Envious-Data/EnvOpenClock/Firmware/display.c

#include <math.h>
#include <stdbool.h>
#include <stdio.h>
#include <stdlib.h>
#include <string.h>

#include "display.h"
#include "hardware/i2c.h"
#include "pico/stdlib.h"

#define I2C_DISPLAY_LINE i2c1
#define I2C_DISPLAY_SDA 26
#define I2C_DISPLAY_SCL 27

#define MODE_ADDR 0b00000000
#define BRIGHTNESS_ADDR 0b00011001
#define UPDATE_ADDR 0b00001100
#define OPTION_ADDR 0b00001101
#define MATRIX_A_ADDR 0b00001110
#define MATRIX_B_ADDR 0b00000001

#define DEFAULT_MODE 0b00011000
#define DEFAULT_OPTIONS 0b00001110

//uint8_t brightness_level = 0b00011001;
uint8_t brightness_level = 0b00111111; // original brightness.


/**
 * @brief The addresses of the displays in order from left to right.
    They are doubled up since there are 2 displays per chip.
 */
uint8_t addresses[8] = {0x63, 0x63, 0x60, 0x60, 0x62, 0x62, 0x61, 0x61};

/**
 * @brief
 *
 */
uint8_t displays[8][8] = {{0b00000000, 0b00000000, 0b00000000, 0b00000000,
                           0b00000000, 0b00000000, 0b00000000, 0b00000000},
                          {0b00000000, 0b00000000, 0b00000000, 0b00000000,
                           0b00000000, 0b00000000, 0b00000000, 0b00000000},
                          {0b00000000, 0b00000000, 0b00000000, 0b00000000,
                           0b00000000, 0b00000000, 0b00000000, 0b00000000},
                          {0b00000000, 0b00000000, 0b00000000, 0b00000000,
                           0b00000000, 0b00000000, 0b00000000, 0b00000000},
                          {0b00000000, 0b00000000, 0b00000000, 0b00000000,
                           0b00000000, 0b00000000, 0b00000000, 0b00000000},
                          {0b00000000, 0b00000000, 0b00000000, 0b00000000,
                           0b00000000, 0b00000000, 0b00000000, 0b00000000},
                          {0b00000000, 0b00000000, 0b00000000, 0b00000000,
                           0b00000000, 0b00000000, 0b00000000, 0b00000000},
                          {0b00000000, 0b00000000, 0b00000000, 0b00000000,
                           0b00000000, 0b00000000, 0b00000000, 0b00000000}};

/**
 * @brief Contains 8x8 bit patterns which correlate to various symbols
    which may need to be displayed on the LTP-305's.

    ASCII Based

    @example
    The symbol "+"
    #Col   1 2 3 4 5
    0b00000000, # Row 1
    0b00000000, # Row 2
    0b00000000, # Row 3
    0b00000000, # Row 4
    0b00000000, # Row 5
    0b00000000, # Row 6
    0b10000000, # Row 7, bit 8 =  decimal place
    0b00000000

    The array { 0x08, 0x08, 0x3e, 0x08, 0x08, 0x00, 0x00, 0x00 }
    0b00001000,
    0b00001000,
    0b00111110,
    0b00001000,
    0b00001000,
    0b00000000,
    0b00000000,
    0b00000000
 */
uint8_t characters[][8] = {
    {0x00, 0x00, 0x00, 0x00, 0x00, 0x00, 0x00, 0x00},  // (space)
    {0x00, 0x00, 0x5f, 0x00, 0x00, 0x00, 0x00, 0x00},  // !
    {0x00, 0x07, 0x00, 0x07, 0x00, 0x00, 0x00, 0x00},  // "
    {0x14, 0x7f, 0x14, 0x7f, 0x14, 0x00, 0x00, 0x00},  // #
    {0x24, 0x2a, 0x7f, 0x2a, 0x12, 0x00, 0x00, 0x00},  // $
    {0x23, 0x13, 0x08, 0x64, 0x62, 0x00, 0x00, 0x00},  // %
    {0x36, 0x49, 0x55, 0x22, 0x50, 0x00, 0x00, 0x00},  // &
    {0x00, 0x05, 0x03, 0x00, 0x00, 0x00, 0x00, 0x00},  // '
    {0x00, 0x1c, 0x22, 0x41, 0x00, 0x00, 0x00, 0x00},  // (
    {0x00, 0x41, 0x22, 0x1c, 0x00, 0x00, 0x00, 0x00},  // )
    {0x08, 0x2a, 0x1c, 0x2a, 0x08, 0x00, 0x00, 0x00},  // *
    {0x08, 0x08, 0x3e, 0x08, 0x08, 0x00, 0x00, 0x00},  // +
    {0x00, 0x50, 0x30, 0x00, 0x00, 0x00, 0x00, 0x00},  // ,
    {0x08, 0x08, 0x08, 0x08, 0x08, 0x00, 0x00, 0x00},  // -
    {0x00, 0x60, 0x60, 0x00, 0x00, 0x00, 0x00, 0x00},  // .
    {0x20, 0x10, 0x08, 0x04, 0x02, 0x00, 0x00, 0x00},  // /
    {0x3e, 0x51, 0x49, 0x45, 0x3e, 0x00, 0x00, 0x00},  // 0
    {0x00, 0x42, 0x7f, 0x40, 0x00, 0x00, 0x00, 0x00},  // 1
    {0x42, 0x61, 0x51, 0x49, 0x46, 0x00, 0x00, 0x00},  // 2
    {0x21, 0x41, 0x45, 0x4b, 0x31, 0x00, 0x00, 0x00},  // 3
    {0x18, 0x14, 0x12, 0x7f, 0x10, 0x00, 0x00, 0x00},  // 4
    {0x27, 0x45, 0x45, 0x45, 0x39, 0x00, 0x00, 0x00},  // 5
    {0x3c, 0x4a, 0x49, 0x49, 0x30, 0x00, 0x00, 0x00},  // 6
    {0x01, 0x71, 0x09, 0x05, 0x03, 0x00, 0x00, 0x00},  // 7
    {0x36, 0x49, 0x49, 0x49, 0x36, 0x00, 0x00, 0x00},  // 8
    {0x06, 0x49, 0x49, 0x29, 0x1e, 0x00, 0x00, 0x00},  // 9
    {0x00, 0x36, 0x36, 0x00, 0x00, 0x00, 0x00, 0x00},  // :
    {0x00, 0x56, 0x36, 0x00, 0x00, 0x00, 0x00, 0x00},  // ;
    {0x00, 0x08, 0x14, 0x22, 0x41, 0x00, 0x00, 0x00},  // <
    {0x14, 0x14, 0x14, 0x14, 0x14, 0x00, 0x00, 0x00},  // =
    {0x41, 0x22, 0x14, 0x08, 0x00, 0x00, 0x00, 0x00},  // >
    {0x02, 0x01, 0x51, 0x09, 0x06, 0x00, 0x00, 0x00},  // ?
    {0x32, 0x49, 0x79, 0x41, 0x3e, 0x00, 0x00, 0x00},  // @
    {0x7e, 0x11, 0x11, 0x11, 0x7e, 0x00, 0x00, 0x00},  // A
    {0x7f, 0x49, 0x49, 0x49, 0x36, 0x00, 0x00, 0x00},  // B
    {0x3e, 0x41, 0x41, 0x41, 0x22, 0x00, 0x00, 0x00},  // C
    {0x7f, 0x41, 0x41, 0x22, 0x1c, 0x00, 0x00, 0x00},  // D
    {0x7f, 0x49, 0x49, 0x49, 0x41, 0x00, 0x00, 0x00},  // E
    {0x7f, 0x09, 0x09, 0x01, 0x01, 0x00, 0x00, 0x00},  // F
    {0x3e, 0x41, 0x41, 0x51, 0x32, 0x00, 0x00, 0x00},  // G
    {0x7f, 0x08, 0x08, 0x08, 0x7f, 0x00, 0x00, 0x00},  // H
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
};

/**
 * @brief In order for characters to be displayed on the second display they
    will need to be translated into the correct bit pattern. This is since
    the first matrix is represented by the 8 byte buffer in the form

    #Col   1 2 3 4 5
    0b00000000, # Row 1
    0b00000000, # Row 2
    0b00000000, # Row 3
    0b00000000, # Row 4
    0b00000000, # Row 5
    0b00000000, # Row 6
    0b10000000, # Row 7, bit 8 =  decimal place
    0b00000000

    This is compared to the second display which is represented as the first
    but reflected in the line y=x.

    #Row 8 7 6 5 4 3 2 1
    0b01111111, # Col 1, bottom to top
    0b01111111, # Col 2
    0b01111111, # Col 3
    0b01111111, # Col 4
    0b01111111, # Col 5
    0b00000000,
    0b00000000,
    0b01000000  # bit 7, decimal place

    To save on processing time these are precalculated at the start of the
    program.
 */
uint8_t alternate_characters[count_of(characters)][8];

/**
 * @brief A helper function to add an amount num_chars to of a specific
 character character_to_append to the end of a string.

    This is used to add whitespace to the end of a scrolling string.
 *
 * @param original The original string to have letters appended to.
 * @param character_to_append The character to append to the string
 * @param num_chars The number of character_to_append to be appended
 *
 * @return char* The new string
 */
char *append_chars(const char *original, char character_to_append,
                   size_t num_chars) {
  size_t original_length = strlen(original);
  char *new_string = (char *)malloc(original_length + num_chars +
                                    1);  // Don't forget +1 for null terminator

  if (new_string == NULL) {
    return NULL;  // Memory allocation failed
  }

  // Copy the original string into the new longer one
  strcpy(new_string, original);

  // Append desired amount of characters
  for (size_t i = 0; i < num_chars; i++) {
    new_string[original_length + i] = character_to_append;
  }

  new_string[original_length + num_chars] = '\0';  // Null-terminate the string

  return new_string;
}

/**
 * @brief This is another helper function that converts an array of
    uint8_t's from a left matrix, the one defined with columns
    v rows into a right matrix in the form rows v columns.

    Essentially this is a reflection in the line y=x of a 2D matrix.
 *
 * @param left_matrix The original matrix in the form columns vs rows
 * @param right_matrix The generated matrix in the form rows vs columns
 */
void convertLeftToRight(const uint8_t *left_matrix, uint8_t *right_matrix) {
  for (int row = 0; row < 8; row++) {
    for (int col = 0; col < 8; col++) {
      uint8_t bit_value = (left_matrix[row] >> (col)) & 1;
      right_matrix[col] |= (bit_value << row);
    }
  }
}

/**
 * @brief This MUST be called at the start of the program otherwise the
    letters for the right matrix will not be generated and will
    not display properly if at all.
 */
void pre_generate_alternate_characters() {
  for (int i = 0; i < count_of(characters); i++) {
    convertLeftToRight(characters[i], alternate_characters[i]);
  }
}

/**
 * @brief Set the option function is used to change a setting on the
    IS31FL3730-QFLS2-TR chips such as brightness or a configuration setting.
 *
 * @param display The 0 indexed display to update [0,8)
 * @param address The address of the register to update on the IS31FL3730
 * @param value The value to send over i2c to the register
 */
void set_option(int display, uint8_t address, uint8_t value) {
  if (display < 0 || display > 7) return;

  uint8_t buf[2];

  buf[0] = address;
  buf[1] = value;

  i2c_write_timeout_us(I2C_DISPLAY_LINE, addresses[display], buf, count_of(buf),
                       false, 1000);
}

/**
 * @brief This is used when updating the displays, in order to update specific
 rows a certain address must be used before the buffer. This function prepends
 this address.
 *
 * @param address The address of the register to be prepended to the start of
 the buffer
 * @param buffer The pointer to the current buffer to have an address prepended
 * @param buffer_size The size of the buffer to be prepended
 *
 * @return uint8_t* The pointer in memory of the new altered buffer
 */
uint8_t *prepend_address(uint8_t address, uint8_t *buffer, int buffer_size) {
  int new_buffer_size = buffer_size + 1;

  uint8_t *new_buffer = (uint8_t *)malloc(new_buffer_size * sizeof(uint8_t));

  if (new_buffer == NULL) {
    return NULL;
  }

  new_buffer[0] = address;

  for (int i = 0; i < buffer_size; i++) {
    new_buffer[i + 1] = buffer[i];
  }

  return new_buffer;
}

/**
 * @brief Used to update all displays all at once. Once called it will push
    what is currently stored in displays to each of the 4 IS31FL3730's
 */
void update_display() {
  // printf("update_display called\n");  // Add this line
  for (int i = 0; i < count_of(displays); i++) {
    uint8_t mat_addr = i % 2 == 0 ? MATRIX_A_ADDR : MATRIX_B_ADDR;

    uint8_t *pre_mat_buf =
        prepend_address(mat_addr, displays[i], count_of(displays[i]));
    i2c_write_timeout_us(I2C_DISPLAY_LINE, addresses[i], pre_mat_buf,
                         count_of(displays[i]) + 1, false, 1000);
    free(pre_mat_buf);

    if (i % 2 != 0) {
      set_option(i, MODE_ADDR, DEFAULT_MODE);
      set_option(i, OPTION_ADDR, DEFAULT_OPTIONS);
      set_option(i, BRIGHTNESS_ADDR, brightness_level);
      set_option(i, UPDATE_ADDR, 0b00000001);
    }
  }
}

/**
 * @brief Set a specific pixel on a display to on or off.
 *
 * @param display The 0 indexed display to update [0,8)
 * @param x The 0 indexed x value of the pixel to be updated [0, 5)
 * @param y The 0 indexed y value of the pixel to be updated [0, 7)
 * @param status Whether the pixel on the LTP305 should be set to on or off
 * @param update Update the display after changing the pixel
 */

void set_pixel(int display, uint8_t x, uint8_t y, bool status, bool update) {
  printf("set_pixel called: display=%d, x=%d, y=%d, status=%d\n", display, x, y,
         status);

  if (display < 0 || display > 7) return;

  if (display % 2 == 0) {
    uint8_t tempX = x;
    x = y;
    y = tempX;
  }

  uint8_t changeVal = 1;
  changeVal <<= x;

  if (status) {
    displays[display][y] |= changeVal;
  } else {
    uint8_t value = displays[display][y];
    value = ~value;
    value |= changeVal;
    value = ~value;
    displays[display][y] = value;
  }

  if (update) {
    uint8_t display_buffer[17];
    display_buffer[0] = 0x00;  // Start at address 0
    convertLeftToRight(displays[display], display_buffer + 1);
    int result = i2c_write_timeout_us(I2C_DISPLAY_LINE, addresses[display],
                                      display_buffer, 17, false,
                                      1000);  // 1000 microsecond timeout
    if (result == PICO_ERROR_TIMEOUT) {
      printf("I2C write timed out in set_pixel!\n");
    } else if (result < 0) {
      printf("I2C write error in set_pixel. Error code: %d\n", result);
    }
  }
}

/**
 * @brief Clear the buffer and reset all values to 0
 *
 * @param update Update the screen after clearing all buffers
 */
void clear_all(bool update) {
  for (int i = 0; i < count_of(displays); i++) {
    for (int j = 0; j < 8; j++) {
      displays[i][j] = 0;
    }
  }

  if (update) update_display();
}

/**
 * @brief Clear a specific display by resetting all values to 0
 *
 * @param display The 0 indexed display to update [0,8)
 * @param update Update the screen after clearing the display buffer
 */
void clear(int display, bool update) {
  if (display < 0 || display > 7) return;
  for (int i = 0; i < 8; i++) {
    displays[display][i] = 0;
  }

  if (update) update_display();
}

/**
 * @brief Transforms a character buffer based on the display number
 * to handle even/odd display differences.
 *
 * @param letter The ASCII character to get the buffer for.
 * @param display The display number.
 * @param buffer The output buffer to store the transformed character.
 */
void transform_buffer_for_display(char letter, int display, uint8_t *buffer) {
  for (int i = 0; i < 8; i++) {
    if (display % 2 == 0) {
      buffer[i] = characters[((int)letter) - 32][i];
    } else {
      buffer[i] = alternate_characters[((int)letter) - 32][i];
    }
  }
}

/**
 * @brief Sets a character to be displayed.
 *
 * @param display The display to set the character on.
 * @param letter The character to set.
 * @param update Whether to update the display immediately.
 */
void set_char(int display, char letter, bool update) {
  if (display < 0 || display > 7) return;
  uint8_t char_buffer[8];
  transform_buffer_for_display(letter, display, char_buffer);
  for (int i = 0; i < 8; i++) {
    displays[display][i] = char_buffer[i];
  }
  if (update) update_display();
}

/**
 * @brief Marque a string across the displays with trailing whitespace
 *
 * @param string The string to be displayed
 */
void scroll_display_string(char *string) {
  string = append_chars(string, ' ', 8);
  int string_length = strlen(string);

  clear_all(false);

  if (string_length > 8) {
    for (int i = 0; i <= string_length - 8; i++) {
      for (int display = 0; display < 8; display++) {
        char char_to_display = string[i + display];
        set_char(display, char_to_display, false);
      }

      update_display();

      if (i == 0) sleep_ms(750);
      sleep_ms(250);
    }

    sleep_ms(2000);
  } else {
    for (int display = 0; display < string_length; display++) {
      set_char(display, string[display], false);
    }
    update_display();
    sleep_ms(2000);
  }

  free(string);
  clear_all(true);
}

/**
 * @brief Set the screen to display the first 6 letters of an ASCII string.
 *
 * @param string The string whose first 6 chars should be displayed.
 */
void display_string(const char *string) {
  clear_all(false);

  for (int i = 0; i < strlen(string); i++) {
    set_char(i, string[i], false);
  }

  update_display();
}

void animate_slide_up(int display, char current_char, char next_char) {
  if (display < 0 || display > 7) return;

  uint8_t current_buffer[8];
  uint8_t next_buffer[8];

  // Get the character bitmaps
  for (int i = 0; i < 8; i++) {
    current_buffer[i] = (display % 2 == 0)
                            ? characters[((int)current_char) - 32][i]
                            : alternate_characters[((int)current_char) - 32][i];
    next_buffer[i] = (display % 2 == 0)
                         ? characters[((int)next_char) - 32][i]
                         : alternate_characters[((int)next_char) - 32][i];
  }

  if (display % 2 == 0) {
    // Even displays: Original vertical slide becomes horizontal (right-to-left)
    for (int shift = 0; shift < 8; shift++) {
      for (int row = 0; row < 8; row++) {
        displays[display][row] =
            (current_buffer[row] >> shift) | (next_buffer[row] << (8 - shift));
      }
      update_display();
      sleep_us(10000);
    }
  } else {
    // Odd displays: Original horizontal slide becomes vertical (bottom-to-top)
    uint8_t offset_current[16];
    uint8_t offset_next[16];

    // Copy to offset buffers, with next buffer on top
    for (int i = 0; i < 8; i++) {
      offset_current[i] = current_buffer[i];
      offset_current[i + 8] = 0;  // Clear the top half
      offset_next[i] = 0;
      offset_next[i + 8] = next_buffer[i];
    }

    // Animation loop (gradually shift)
    for (int shift = 0; shift < 8; shift++) {
      // Copy the animation into the display buffer
      for (int row = 0; row < 8; row++) {
        displays[display][row] =
            offset_current[row + shift] | offset_next[row + shift];
      }

      update_display();
      sleep_us(10000);  // Adjust animation speed
    }
  }

  // Final update with the next character
  set_char(display, next_char, true);
}

void animate_pixelated_transition(int display, char current_char,
                                 char next_char) {
  if (display < 0 || display > 7) return;

  uint8_t current_buffer[8];
  uint8_t next_buffer[8];
  uint8_t temp_buffer[8];  // For pixel manipulation

  // Get character bitmaps
  for (int i = 0; i < 8; i++) {
    current_buffer[i] = (display % 2 == 0)
                            ? characters[((int)current_char) - 32][i]
                            : alternate_characters[((int)current_char) - 32][i];
    next_buffer[i] = (display % 2 == 0)
                         ? characters[((int)next_char) - 32][i]
                         : alternate_characters[((int)next_char) - 32][i];
  }

  // Pixelated dissolve animation
  for (int step = 0; step < 8; step++) {
    for (int row = 0; row < 8; row++) {
      temp_buffer[row] = 0;
      for (int col = 0; col < 8; col++) {
        int rand_val = rand() % (8 - step);
        if (display % 2 == 0) {
          // Even displays: Standard pixelated transition
          if (rand_val == 0) {  // Randomly choose pixels
            temp_buffer[row] |= (next_buffer[row] & (1 << col));
          } else {
            temp_buffer[row] |= (current_buffer[row] & (1 << col));
          }
        } else {
          // Odd displays: Horizontal pixelated transition
          if (rand_val == 0) {
            temp_buffer[row] |= (next_buffer[row] & (1 << (7 - col)));
          } else {
            temp_buffer[row] |= (current_buffer[row] & (1 << (7 - col)));
          }
        }
      }
      displays[display][row] = temp_buffer[row];
    }
    update_display();
    sleep_us(10000);  // Adjust animation speed
  }

  // Final update
  set_char(display, next_char, true);
}

void animate_expanding_contracting(int display, char current_char,
                                   char next_char) {
  if (display < 0 || display > 7) return;

  uint8_t current_buffer[8];
  uint8_t next_buffer[8];
  uint8_t temp_buffer[8];

  // Get character bitmaps
  for (int i = 0; i < 8; i++) {
    current_buffer[i] = (display % 2 == 0)
                            ? characters[((int)current_char) - 32][i]
                            : alternate_characters[((int)current_char) - 32][i];
    next_buffer[i] = (display % 2 == 0)
                         ? characters[((int)next_char) - 32][i]
                         : alternate_characters[((int)next_char) - 32][i];
  }

  // Expanding animation (simplified)
  for (int scale = 1; scale <= 8; scale++) {
    for (int row = 0; row < 8; row++) {
      temp_buffer[row] = 0;
      for (int col = 0; col < 8; col++) {
        if ((next_buffer[row] & (1 << col)) &&
            (col % scale == 0 && row % scale == 0)) {
          temp_buffer[row] |= (1 << col);
        }
      }
      displays[display][row] = temp_buffer[row];
    }
    update_display();
    sleep_us(10000);  // Adjust animation speed
  }

  // Final update
  set_char(display, next_char, true);
}

void animate_morph(int display, char current_char, char next_char) {
  if (display < 0 || display > 7) return;

  uint8_t current_buffer[8];
  uint8_t next_buffer[8];
  uint8_t morph_buffer[8];

  // Get character bitmaps
  for (int i = 0; i < 8; i++) {
    current_buffer[i] = (display % 2 == 0)
                            ? characters[((int)current_char) - 32][i]
                            : alternate_characters[((int)current_char) - 32][i];
    next_buffer[i] = (display % 2 == 0)
                         ? characters[((int)next_char) - 32][i]
                         : alternate_characters[((int)next_char) - 32][i];
  }

  // Morphing animation (simplified)
  for (int step = 0; step <= 8; step++) {
    for (int row = 0; row < 8; row++) {
      morph_buffer[row] =
          (current_buffer[row] & ~(next_buffer[row] & ((1 << step) - 1))) |
          (next_buffer[row] & ((1 << step) - 1));
      displays[display][row] = morph_buffer[row];
    }
    update_display();
    sleep_us(10000);  // Adjust animation speed
  }

  // Final update
  set_char(display, next_char, true);
}

void animate_interlocking_pieces(int display, char current_char,
                                 char next_char) {
  if (display < 0 || display > 7) return;

  uint8_t current_buffer[8];
  uint8_t next_buffer[8];

  // Get character bitmaps
  for (int i = 0; i < 8; i++) {
    current_buffer[i] = (display % 2 == 0)
                            ? characters[((int)current_char) - 32][i]
                            : alternate_characters[((int)current_char) - 32][i];
    next_buffer[i] = (display % 2 == 0)
                         ? characters[((int)next_char) - 32][i]
                         : alternate_characters[((int)next_char) - 32][i];
  }

  // Animation: Slide in from edges
  for (int step = 0; step < 4; step++) {
    for (int row = 0; row < 8; row++) {
      if (display % 2 == 0) {
        // Even displays: Top and bottom slide
        if (row < 4) {
          // Top half slides down
          displays[display][row] =
              (current_buffer[row] << (4 - step)) | (next_buffer[row] >> step);
        } else {
          // Bottom half slides up
          displays[display][row] =
              (current_buffer[row] >> (4 - step)) | (next_buffer[row] << step);
        }
      } else {
        // Odd displays: Left and right slide (rotated 90 degrees)
        // Treat columns as rows and rows as columns
        if (row < 4) {
          displays[display][row] =
              (current_buffer[row] >> (4 - step)) | (next_buffer[row] << step);
        } else {
          displays[display][row] =
              (current_buffer[row] << (4 - step)) | (next_buffer[row] >> step);
        }
      }
    }
    update_display();
    sleep_us(10000);  // Adjust speed as needed
  }

  // Final update
  set_char(display, next_char, true);
}

void animate_glitch_effect(int display, char current_char, char next_char) {
  if (display < 0 || display > 7) return;

  uint8_t current_buffer[8];
  uint8_t next_buffer[8];
  uint8_t glitch_buffer[8];

  // Get the character bitmaps
  for (int i = 0; i < 8; i++) {
    current_buffer[i] = (display % 2 == 0)
                            ? characters[((int)current_char) - 32][i]
                            : alternate_characters[((int)current_char) - 32][i];
    next_buffer[i] = (display % 2 == 0)
                         ? characters[((int)next_char) - 32][i]
                         : alternate_characters[((int)next_char) - 32][i];
  }

  // Initial state
  for (int row = 0; row < 8; row++) {
    displays[display][row] = current_buffer[row];
  }
  update_display();
  sleep_us(10000);

  // Random seed based on time
  srand(time_us_32());

  // Three glitch frames
  for (int frame = 0; frame < 3; frame++) {
    // Create a glitched frame
    for (int i = 0; i < 8; i++) {
      glitch_buffer[i] = 0; // Initialize glitch buffer

      for (int col = 0; col < 5; col++) { // Iterate through columns
        // Mix between current, next, and random noise
        if (rand() % 3 == 0) {
          // Random noise - only use lower 5 bits for 5×7 display
          if (display % 2 == 0) {
            glitch_buffer[i] |= (rand() % 32) & (1 << col);
          } else {
            glitch_buffer[i] |= (rand() % 32) & (1 << (4 - col));
          }
        } else if (rand() % 2) {
          // Current with horizontal shift
          int shift = (rand() % 3) - 1; // -1, 0, or 1
          uint8_t shifted = shift > 0 ? (current_buffer[i] << shift)
                                      : (current_buffer[i] >> -shift);
          if (display % 2 == 0) {
            glitch_buffer[i] |= (shifted & 0x1F) & (1 << col);
          } else {
            glitch_buffer[i] |= (shifted & 0x1F) & (1 << (4 - col));
          }
        } else {
          // Next char with some bits flipped
          uint8_t flipped = next_buffer[i] ^ (1 << (rand() % 5));
          if (display % 2 == 0) {
            glitch_buffer[i] |= (flipped & 0x1F) & (1 << col);
          } else {
            glitch_buffer[i] |= (flipped & 0x1F) & (1 << (4 - col));
          }
        }
      }

      // Sometimes swap rows (apply to both even and odd)
      if (i > 0 && rand() % 5 == 0) {
        uint8_t temp = glitch_buffer[i];
        glitch_buffer[i] = glitch_buffer[i - 1];
        glitch_buffer[i - 1] = temp;
      }
    }

    // Display the glitch frame
    for (int row = 0; row < 8; row++) {
      displays[display][row] = glitch_buffer[row];
    }
    update_display();

    // Random short duration for the glitch
    sleep_us(10000 + (rand() % 16600));
  }

  // Quick flash of blank display
  for (int row = 0; row < 8; row++) {
    displays[display][row] = 0;
  }
  update_display();
  sleep_us(10000);

  // Final reveal of next character
  set_char(display, next_char, true);
}

void animate_heartbeat_pulse(int display, char current_char, char next_char) {
  if (display < 0 || display > 7) return;

  uint8_t current_buffer[8];
  uint8_t next_buffer[8];
  uint8_t temp_buffer[8];

  // Get the character bitmaps
  for (int i = 0; i < 8; i++) {
    current_buffer[i] = (display % 2 == 0)
                            ? characters[((int)current_char) - 32][i]
                            : alternate_characters[((int)current_char) - 32][i];
    next_buffer[i] = (display % 2 == 0)
                         ? characters[((int)next_char) - 32][i]
                         : alternate_characters[((int)next_char) - 32][i];
  }

  // First pulse - fade out current character slightly
  for (int i = 0; i < 8; i++) {
    // For 5×7 display, only use lower 5 bits
    temp_buffer[i] =
        current_buffer[i] & 0x15;  // Remove some pixels (binary 00010101)
  }

  for (int row = 0; row < 8; row++) {
    displays[display][row] = temp_buffer[row];
  }
  update_display();
  sleep_us(10000);  // Quick dimming

  // Restore original
  for (int row = 0; row < 8; row++) {
    displays[display][row] = current_buffer[row];
  }
  update_display();
  sleep_us(10000);

  // Second pulse - stronger fade
  for (int i = 0; i < 8; i++) {
    // For 5×7 display, only use lower 5 bits
    temp_buffer[i] =
        current_buffer[i] & 0x09;  // Remove more pixels (binary 00001001)
  }

  for (int row = 0; row < 8; row++) {
    displays[display][row] = temp_buffer[row];
  }
  update_display();
  sleep_us(10000);  // Slightly longer

  // Transition to next character with quick fade in
  for (int i = 0; i < 8; i++) {
    temp_buffer[i] = next_buffer[i] & 0x09;  // Start with sparse pixels
  }

  for (int row = 0; row < 8; row++) {
    displays[display][row] = temp_buffer[row];
  }
  update_display();
  sleep_us(10000);

  // Medium density
  for (int i = 0; i < 8; i++) {
    temp_buffer[i] = next_buffer[i] & 0x15;  // Medium density pixels
  }

  for (int row = 0; row < 8; row++) {
    displays[display][row] = temp_buffer[row];
  }
  update_display();
  sleep_us(10000);

  // Final reveal of next character
  set_char(display, next_char, true);
}

void animate_waterfall(int display, char current_char, char next_char) {
  if (display < 0 || display > 7) return;

  uint8_t current_buffer[8];
  uint8_t next_buffer[8];
  uint8_t anim_buffer[8];

  // Get character bitmaps, considering even/odd displays
  for (int i = 0; i < 8; i++) {
    if (display % 2 == 0) {
      current_buffer[i] = characters[((int)current_char) - 32][i];
      next_buffer[i] = characters[((int)next_char) - 32][i];
    } else {
      current_buffer[i] = alternate_characters[((int)current_char) - 32][i];
      next_buffer[i] = alternate_characters[((int)next_char) - 32][i];
    }
  }

  // Start with empty animation buffer
  for (int i = 0; i < 8; i++) {
    anim_buffer[i] = 0;
  }

  // Flow down animation - reveal the next character from top to bottom
  for (int frame = 0; frame < 8; frame++) {
    for (int row = 0; row < 8; row++) {
      if (display % 2 == 0) {
        // Even displays - Left-to-right horizontal waterfall
        anim_buffer[row] = 0;
        // Add black pixel line before wipe
        if (frame > 0) {
          for (int col = 0; col < 8; col++) {
            if (col == frame - 1) {
              //  Clear this column to create a black line
              anim_buffer[row] &= ~(1 << col);
            }
            if (col <= frame) {
              if (next_buffer[row] & (1 << col)) {
                anim_buffer[row] |= (1 << col);
              }
            } else {
              if (current_buffer[row] & (1 << col)) {
                anim_buffer[row] |= (1 << col);
              }
            }
          }
        } else {
          for (int col = 0; col < 8; col++) {
            if (col <= frame) {
              if (next_buffer[row] & (1 << col)) {
                anim_buffer[row] |= (1 << col);
              }
            } else {
              if (current_buffer[row] & (1 << col)) {
                anim_buffer[row] |= (1 << col);
              }
            }
          }
        }
      } else {
        // Odd displays - Top-to-bottom vertical waterfall
        // Add black pixel line before wipe
        if (frame > 0) {
          // Clear this row to create a black line
          if (row == frame - 1) {
            anim_buffer[row] = 0x00;
          } else if (row <= frame) {
            anim_buffer[row] = next_buffer[row];
          } else {
            anim_buffer[row] = current_buffer[row];
          }
        } else {
          if (row <= frame) {
            anim_buffer[row] = next_buffer[row];
          } else {
            anim_buffer[row] = current_buffer[row];
          }
        }
      }
    }

    // Display the animation frame
    for (int row = 0; row < 8; row++) {
      displays[display][row] = anim_buffer[row];
    }
    update_display();
    sleep_us(8000);
  }

  // Final state
  set_char(display, next_char, true);
}

// Clock hand wipe - simulates analog clock hand expanding dot with controlled reveal
void animate_clock_hand_wipe(int display, char current_char, char next_char) {
  if (display < 0 || display > 7) return;

  uint8_t current_buffer[8];
  uint8_t next_buffer[8];
  uint8_t anim_buffer[8];

  // Get character bitmaps
  for (int i = 0; i < 8; i++) {
    current_buffer[i] = (display % 2 == 0)
                            ? characters[((int)current_char) - 32][i]
                            : alternate_characters[((int)current_char) - 32][i];
    next_buffer[i] = (display % 2 == 0)
                         ? characters[((int)next_char) - 32][i]
                         : alternate_characters[((int)next_char) - 32][i];
  }

  // Define center of the effect
  const float center_x = 2.0;
  const float center_y = 3.5;

  // Animation loop (radius expansion)
  for (int radius = 0; radius <= 4; radius++) {
    // Clear the animation buffer
    for (int i = 0; i < 8; i++) {
      anim_buffer[i] = 0;
    }

    // (Optional) Initial Clear - very brief
    if (radius == 0) {
      for (int row = 0; row < 8; row++) {
        displays[display][row] = 0x00;
      }
      update_display();
      sleep_us(2000); // Very short clear
    }

    // For each pixel position
    for (int row = 0; row < 8; row++) {
      for (int col = 0; col < 5; col++) {
        // Calculate pixel position relative to center
        float dx = col - center_x;
        float dy = row - center_y;

        // Calculate distance from center
        float dist = sqrt(dx * dx + dy * dy);

        // If this pixel is within the expanding radius
        if (dist <= radius) {
          // Controlled Reveal: Prioritize next_buffer
          uint8_t bit_mask = (1 << col);
          if (next_buffer[row] & bit_mask) {
            anim_buffer[row] |= bit_mask;
          } else if (radius < 4 && current_buffer[row] & bit_mask) {
            //  Only show old character within a smaller radius
            //  This helps "mask" the old character
            if (dist <= radius -1)
            {
              anim_buffer[row] |= bit_mask;
            }
          }
           else if (radius == 4)
           {
             anim_buffer[row] |= next_buffer[row] & bit_mask;
           }
        }
      }
    }

    // Display animation frame
    for (int row = 0; row < 8; row++) {
      displays[display][row] = anim_buffer[row];
    }
    update_display();
    sleep_us(25000); // Adjust for speed as needed
  }

  // Final state
  set_char(display, next_char, true);
}
